DLaxV-Community-Projects-Hub/Open-Shot-Clock/cad/horn_cuff_looser.step

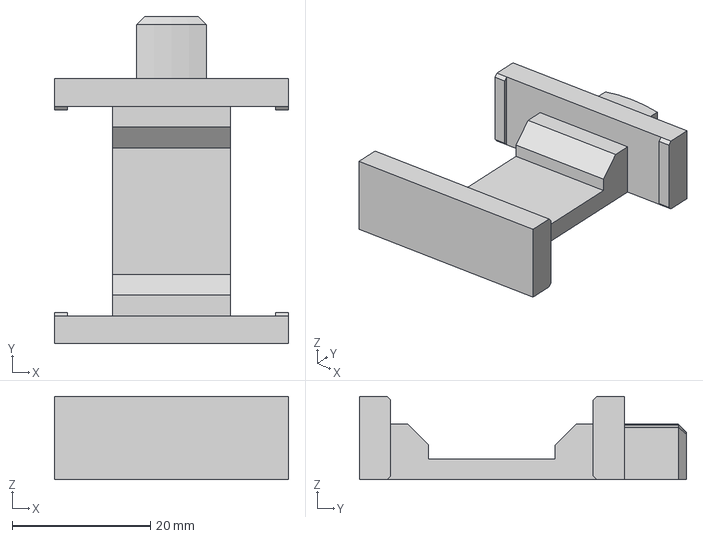
[picture p58: CAD file, 2024-12-09]
cad/horn_cuff_looser.step
33.8 x 47.3 x 12.0 mm
