DLaxV-Community-Projects-Hub/Open-Shot-Clock/documentation/3dprinting_files/Tripod_Flang_8mm_Base_Plate.3mf

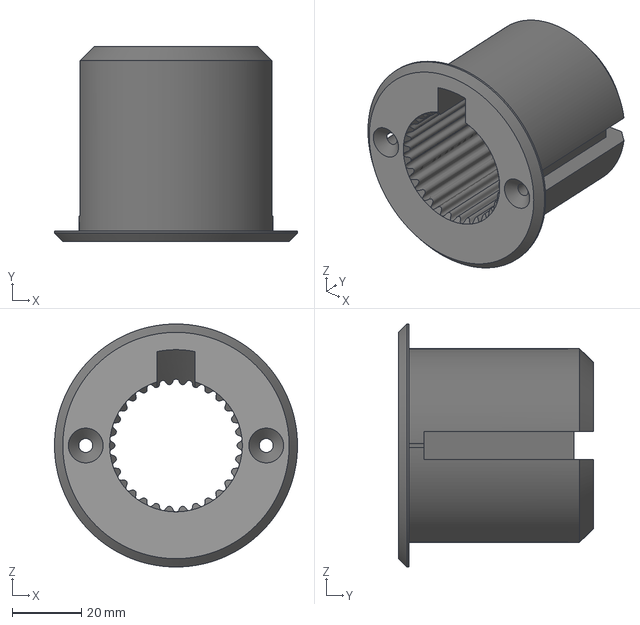
[picture p59: CAD file, 2023-03-31]
documentation/3dprinting_files/Tripod_Flang_8mm_Base_Plate.3mf
70.0 x 56.2 x 70.0 mm
