DLaxV-Community-Projects-Hub/Open-Shot-Clock/cad/Junction_Case_Mark3 v1.step

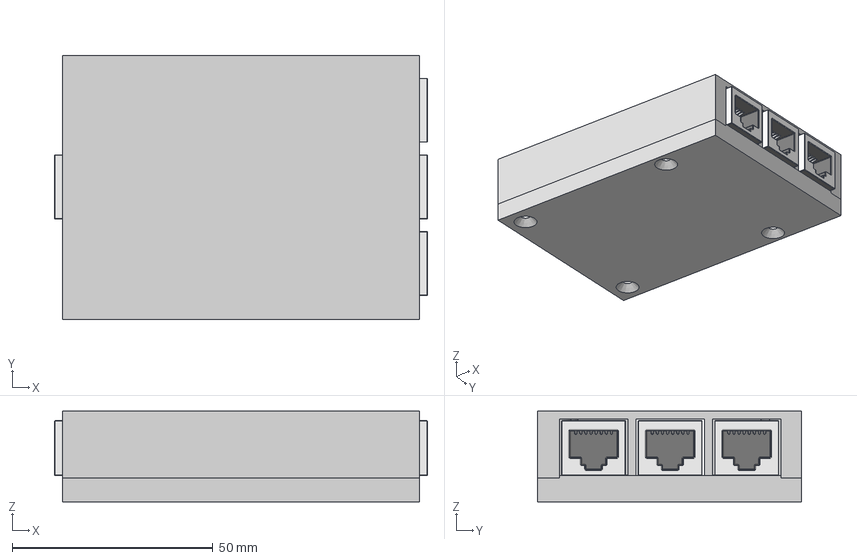
[picture p61: CAD file, 2023-01-02]
cad/Junction_Case_Mark3 v1.step
92.8 x 65.6 x 22.6 mm
junction_top
junction_bottom
Board
OPEN-SHOT-CLOCK-LOGO-H50MM
OPEN-SHOT-CLOCK-LOGO-SMALL
RS485-TTL x 3
