DLaxV-Community-Projects-Hub/Open-Shot-Clock/documentation/3dprinting_files/Tripod_Flange_Insert_8mm_base_plate.3mf

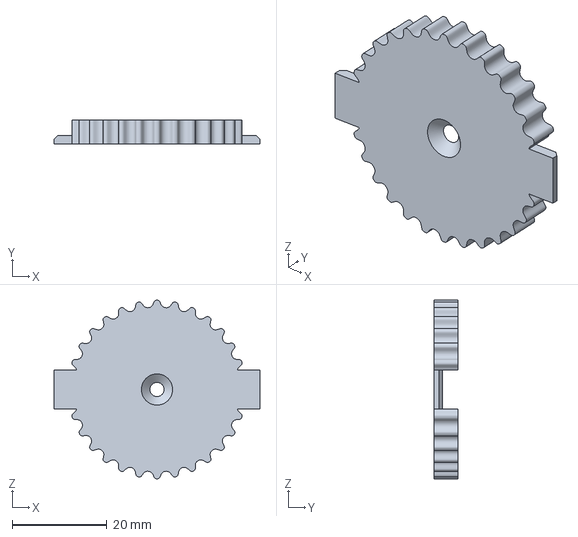
[picture p62: CAD file, 2023-03-31]
documentation/3dprinting_files/Tripod_Flange_Insert_8mm_base_plate.3mf
43.6 x 5.00 x 37.8 mm
