DLaxV-Community-Projects-Hub/Open-Shot-Clock/documentation/3dprinting_files/Upper_Controller_Shell.3mf

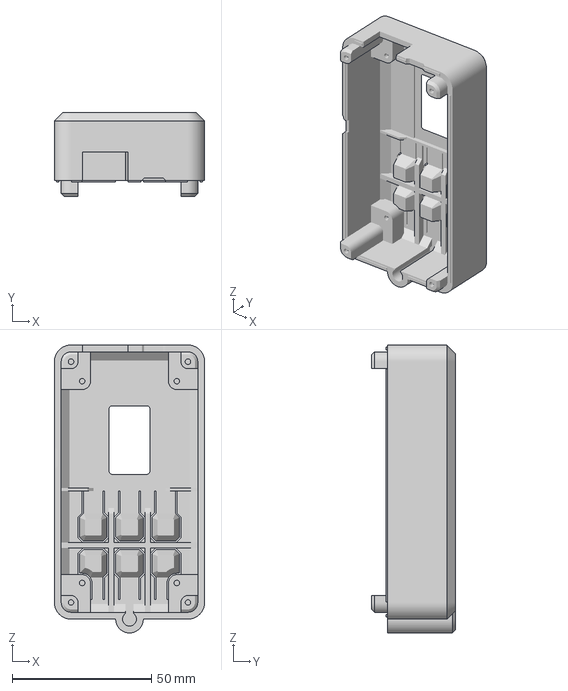
[picture p63: CAD file, 2023-01-02]
documentation/3dprinting_files/Upper_Controller_Shell.3mf
54.0 x 30.0 x 103.5 mm
