DLaxV-Community-Projects-Hub/Open-Shot-Clock/documentation/3dprinting_files/Lower_Controller_Shell.3mf

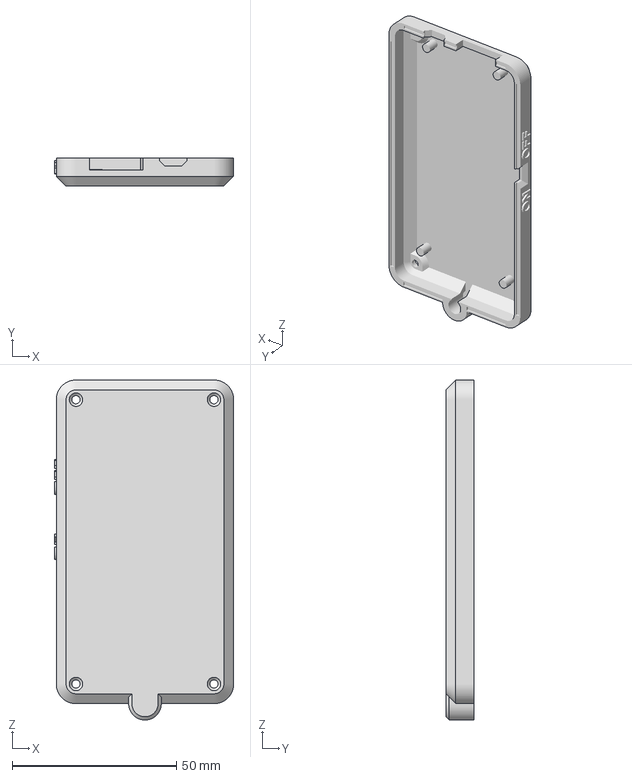
[picture p64: CAD file, 2023-01-02]
documentation/3dprinting_files/Lower_Controller_Shell.3mf
54.6 x 8.60 x 103.5 mm
