DLaxV-Community-Projects-Hub/Open-Shot-Clock/documentation/3dprinting_files/Socket_Plate.3mf

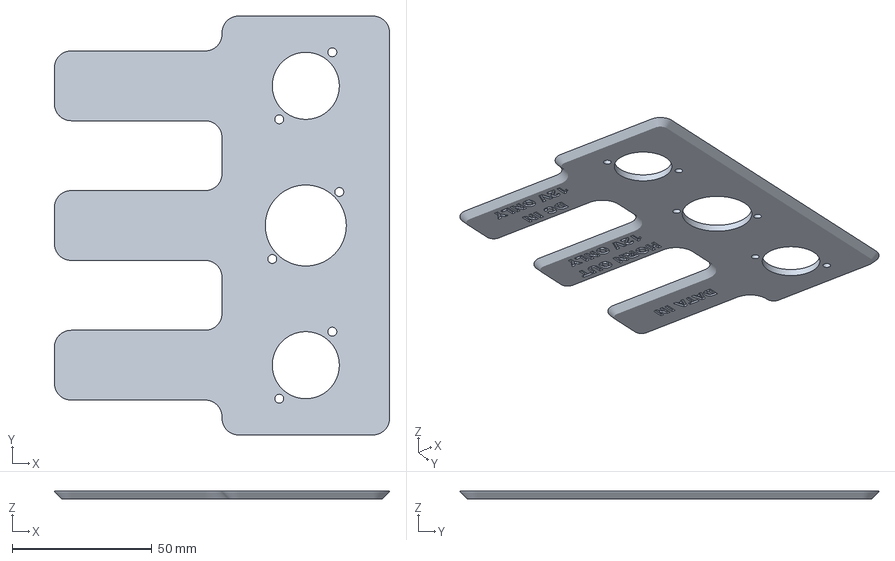
[picture p65: CAD file, 2023-01-02]
documentation/3dprinting_files/Socket_Plate.3mf
120.0 x 150.0 x 2.90 mm
