DLaxV-Community-Projects-Hub/Open-Shot-Clock/documentation/3dprinting_files/Ventilation_Grid.3mf

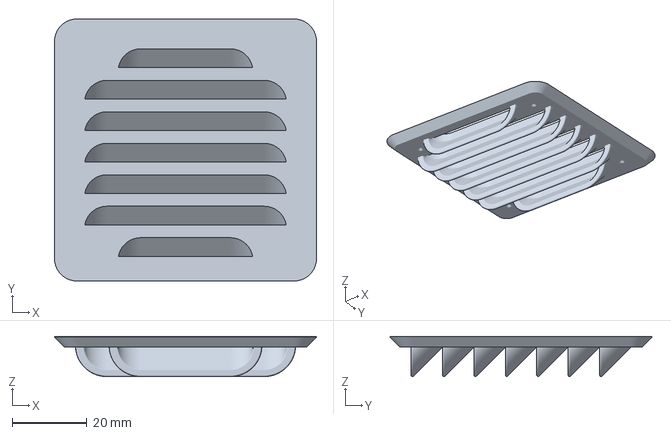
[picture p66: CAD file, 2023-01-02]
documentation/3dprinting_files/Ventilation_Grid.3mf
70.0 x 70.0 x 10.7 mm
