DLaxV-Community-Projects-Hub/Open-Shot-Clock/documentation/3dprinting_files/Antenna_Bracket.3mf

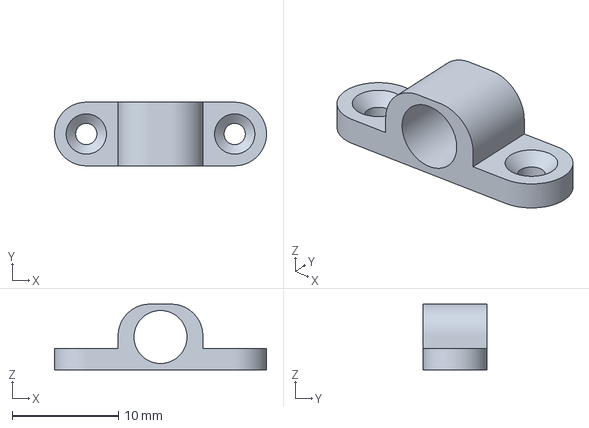
[picture p67: CAD file, 2023-01-02]
documentation/3dprinting_files/Antenna_Bracket.3mf
20.0 x 6.00 x 6.20 mm
