DLaxV-Community-Projects-Hub/Open-Shot-Clock/documentation/3dprinting_files/Round_Sealing_Hinge.3mf

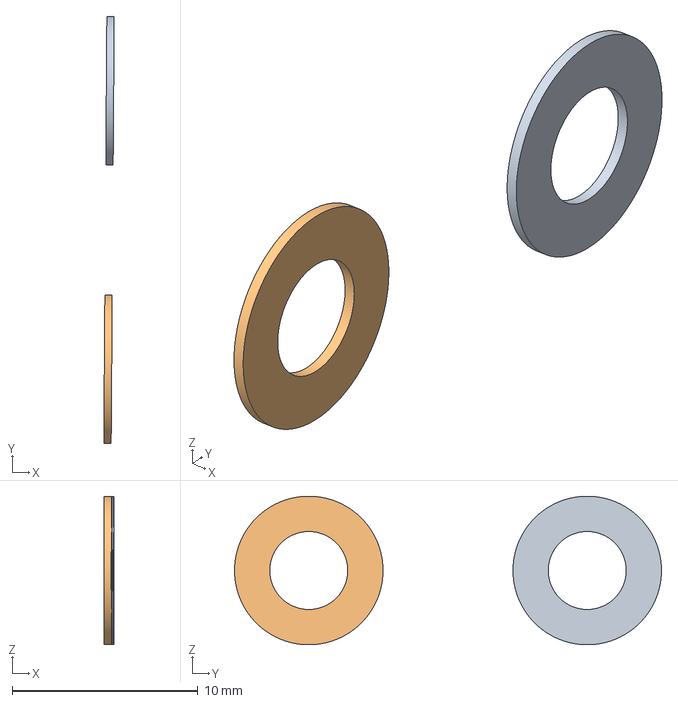
[picture p68: CAD file, 2023-01-02]
documentation/3dprinting_files/Round_Sealing_Hinge.3mf
0.565 x 23.0 x 8.00 mm
Körper1
Körper2
