DLaxV-Community-Projects-Hub/Open-Shot-Clock/documentation/3dprinting_files/Upper_Junction_Case.3mf

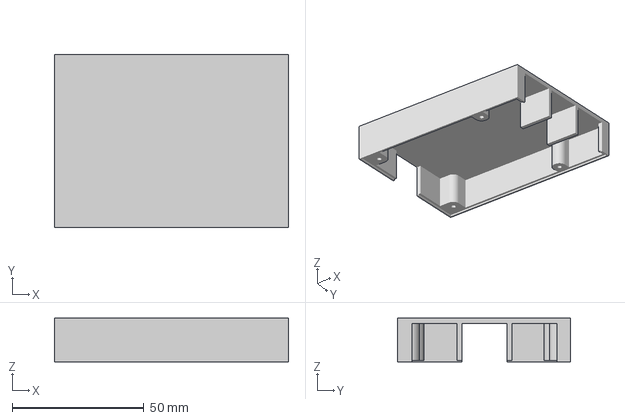
[picture p69: CAD file, 2023-01-02]
documentation/3dprinting_files/Upper_Junction_Case.3mf
88.8 x 65.6 x 16.6 mm
