DLaxV-Community-Projects-Hub/Open-Shot-Clock/documentation/3dprinting_files/Sealing_Corner_Joint.3mf

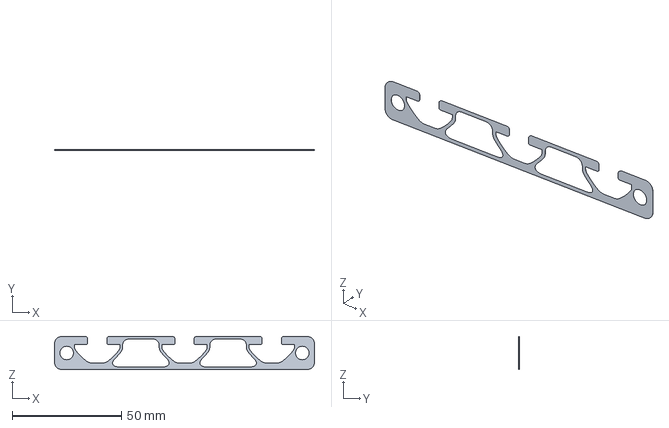
[picture p70: CAD file, 2023-01-02]
documentation/3dprinting_files/Sealing_Corner_Joint.3mf
119.2 x 0.4 x 15.2 mm
