DLaxV-Community-Projects-Hub/Open-Shot-Clock/documentation/3dprinting_files/Upper_Corner_Joint.3mf

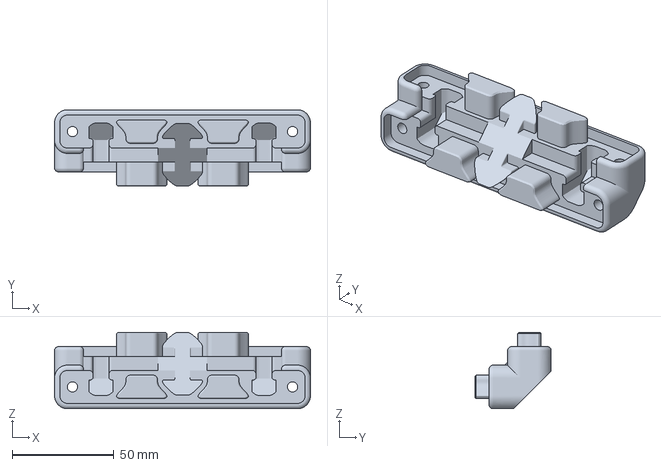
[picture p71: CAD file, 2023-01-02]
documentation/3dprinting_files/Upper_Corner_Joint.3mf
125.6 x 37.5 x 37.5 mm
