DLaxV-Community-Projects-Hub/Open-Shot-Clock/documentation/3dprinting_files/Type_Plate_no_Orga_Set1_No1.3mf

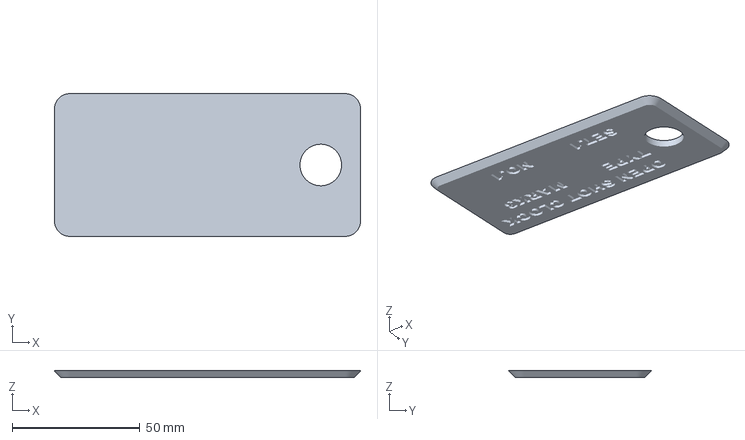
[picture p73: CAD file, 2023-01-02]
documentation/3dprinting_files/Type_Plate_no_Orga_Set1_No1.3mf
120.0 x 56.0 x 2.90 mm
