DLaxV-Community-Projects-Hub/Open-Shot-Clock/documentation/3dprinting_files/PCB_Stand_Offs.3mf

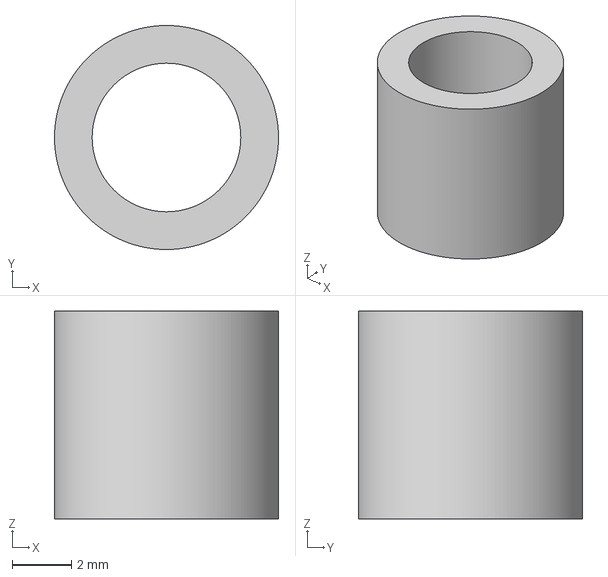
[picture p74: CAD file, 2023-01-02]
documentation/3dprinting_files/PCB_Stand_Offs.3mf
7.54 x 7.54 x 7.00 mm
