DLaxV-Community-Projects-Hub/Open-Shot-Clock/documentation/3dprinting_files/Round_Sealing_Corner_Joint.3mf

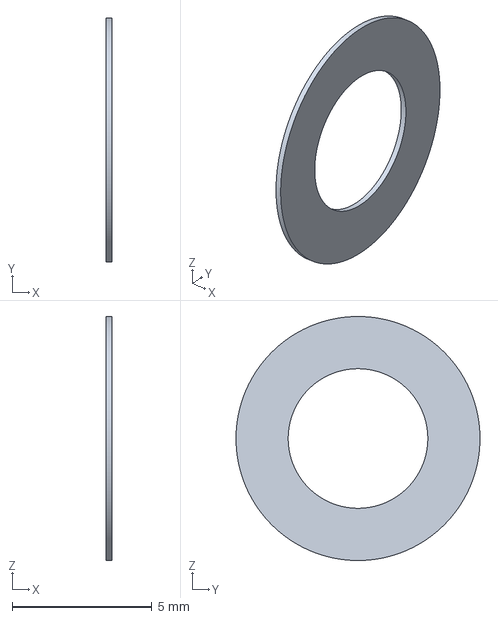
[picture p75: CAD file, 2023-01-02]
documentation/3dprinting_files/Round_Sealing_Corner_Joint.3mf
0.2 x 8.74 x 8.74 mm
