DLaxV-Community-Projects-Hub/Open-Shot-Clock/documentation/3dprinting_files/Lower_Corner_Joint.3mf

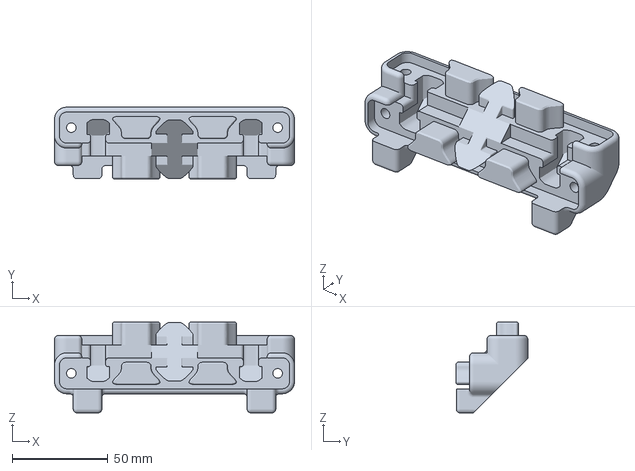
[picture p76: CAD file, 2023-01-02]
documentation/3dprinting_files/Lower_Corner_Joint.3mf
125.6 x 37.5 x 47.5 mm
