DLaxV-Community-Projects-Hub/Open-Shot-Clock/documentation/3dprinting_files/Sealing_Hinge.3mf

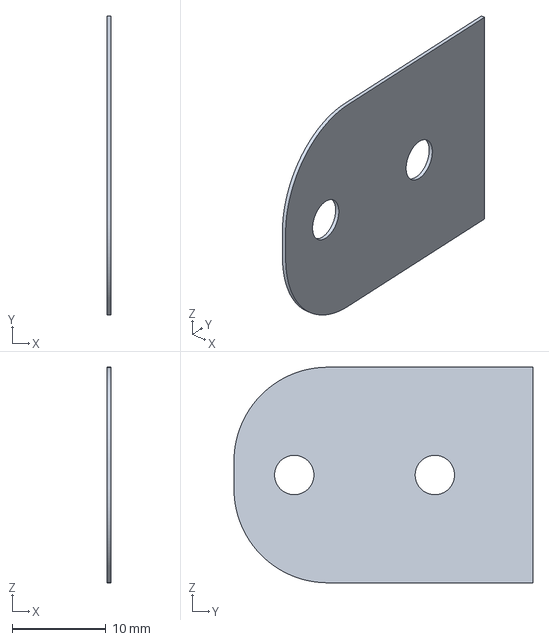
[picture p77: CAD file, 2023-01-02]
documentation/3dprinting_files/Sealing_Hinge.3mf
0.4 x 31.9 x 23.0 mm
