DLaxV-Community-Projects-Hub/Open-Shot-Clock/documentation/drawings/7_Extrusion_Profile_Bottom_Drawing.pdf

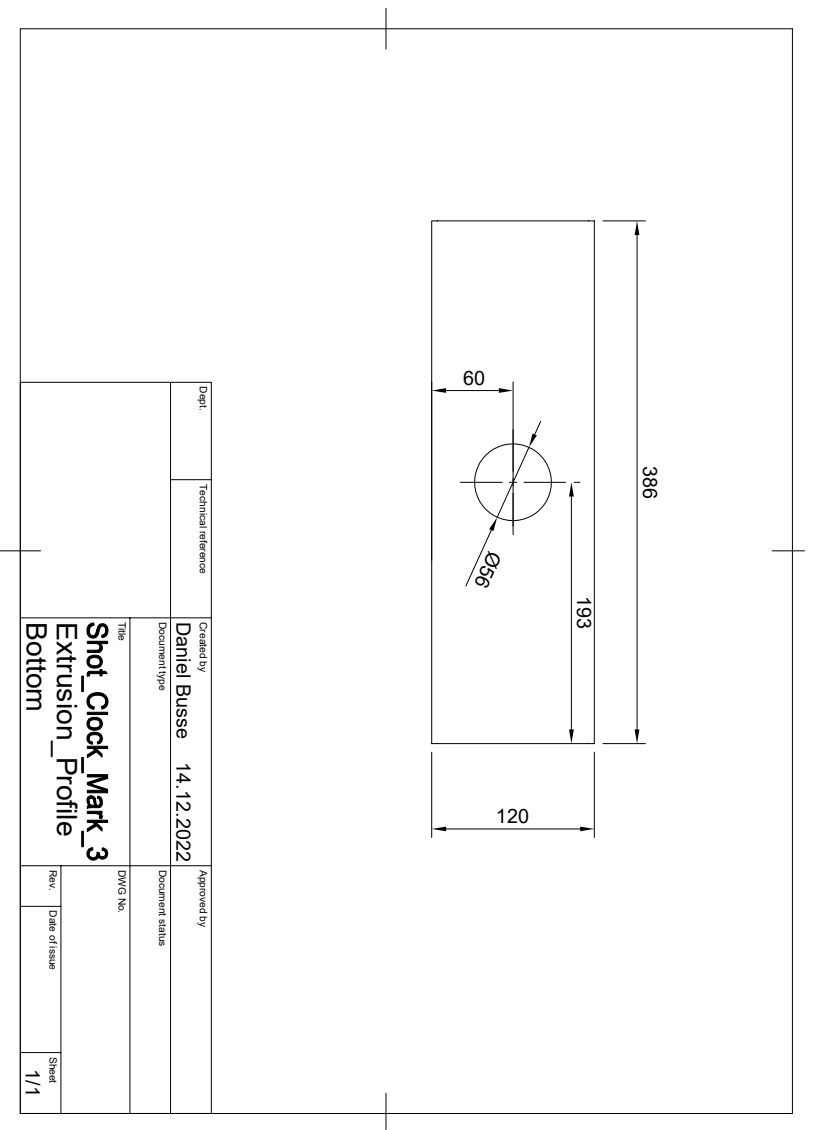
[picture p115: page 1]

Dept. Technical reference Created by Approved by Title DWG No. Document type Document status Rev. Date of issue Sheet Bottom 14.12.2022 1/1 Extrusion_Profile Daniel Busse
